fmash16/SHO/pictures/2.jpeg

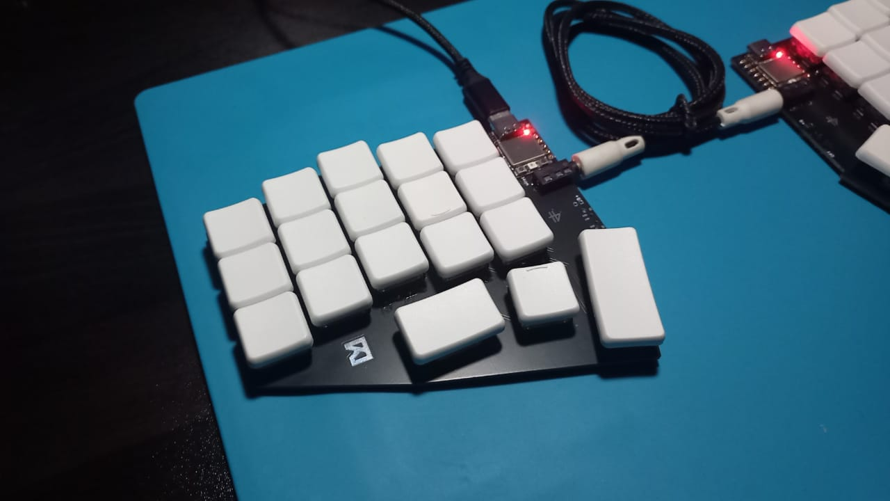
pictures/2.jpeg
