fmash16/SHO/pictures/3.jpeg

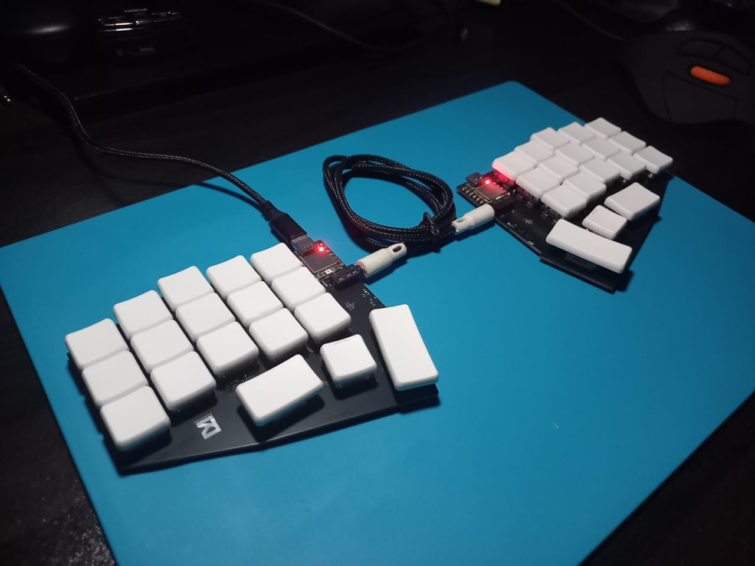
pictures/3.jpeg
