fmash16/SHO/pictures/4.jpeg

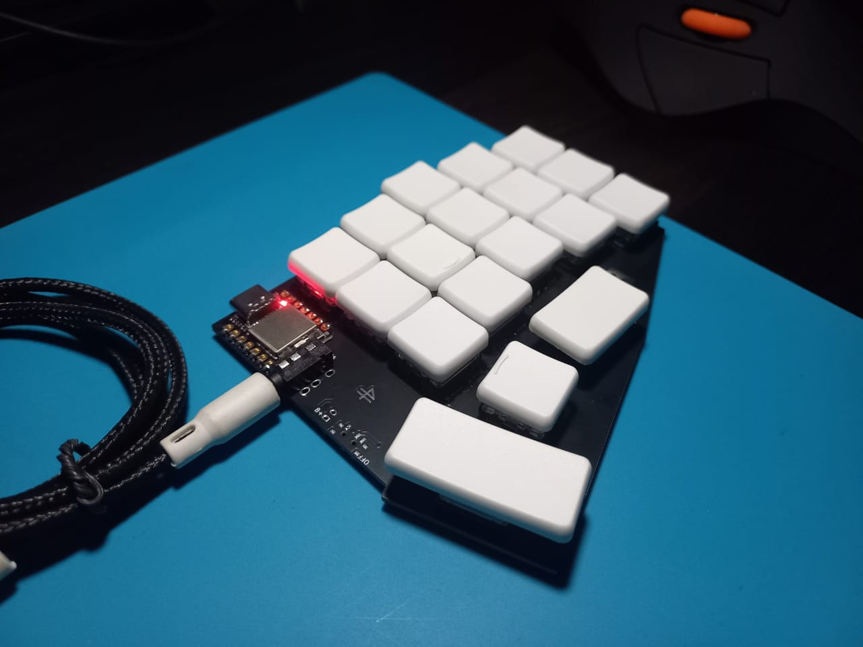
pictures/4.jpeg
