fmash16/SHO/pictures/5.jpeg

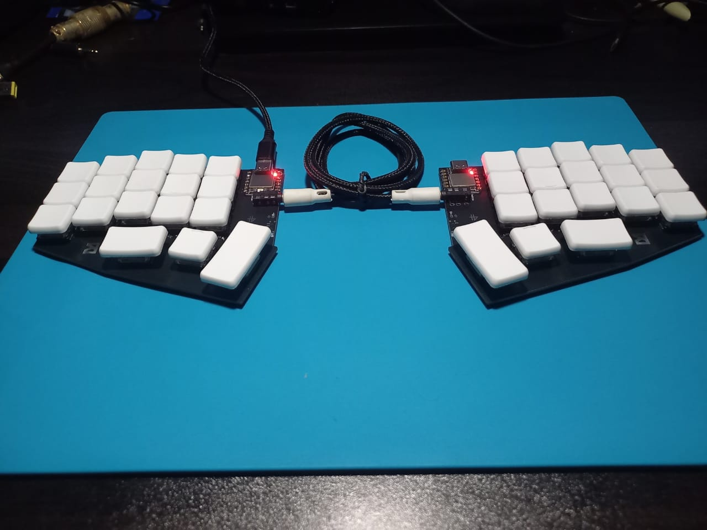
pictures/5.jpeg
