fmash16/SHO/pictures/6.jpeg

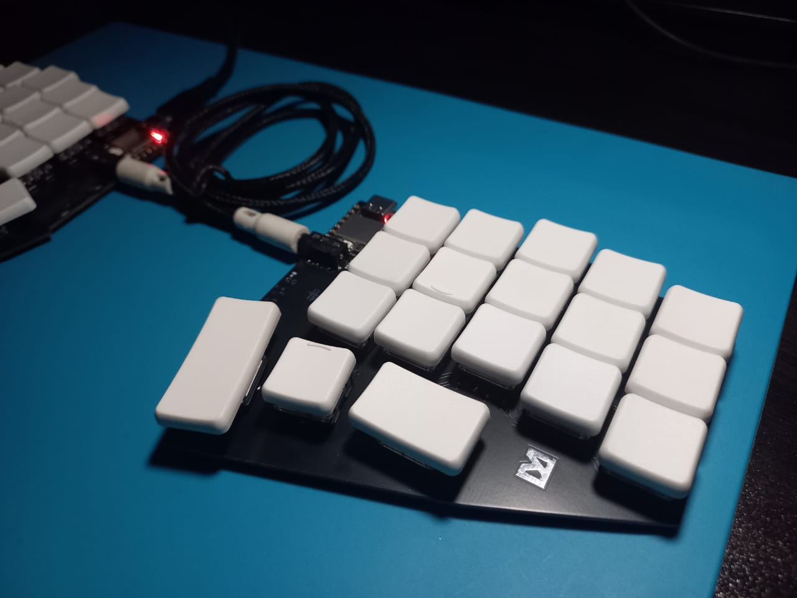
pictures/6.jpeg
